bluetiger9/SmartElectronicLoad/Firmware/src/hw.cpp

#include "hw.h"

float HardwareValues::loadVoltageAdcMultiplier1;

float HardwareValues::loadVoltageAdcMultiplier2;

float HardwareValues::currentSenseAdcMultiplier;

float HardwareValues::currentSetDacMultiplier;
