bluetiger9/SmartElectronicLoad/Firmware/src/ota.h

/*
 * Copyright (c) 2025 by Attila Tőkés.
 *
 * Licence: MIT
 */
#ifndef OTA_H
#define OTA_H

#include <ArduinoOTA.h>

/** Handles Over-the-Air (OTA) firmware updates */
class OTA {
public:
  void begin() {
    Serial.println("Setting up OTA!");

    ArduinoOTA
      .onStart([]() {
        String type;
        if (ArduinoOTA.getCommand() == U_FLASH) {
            type = "sketch";
        } else {  // U_SPIFFS
            type = "filesystem";
        }

        // NOTE: if updating SPIFFS this would be the place to unmount SPIFFS using SPIFFS.end()
        Serial.println("Start updating " + type);
      })
      .onEnd([]() {
        Serial.println("\nEnd");
      })
      .onProgress([](unsigned int progress, unsigned int total) {
        if ((progress % 10 == 0) || (progress > 90)) {
          Serial.printf("Progress: %u%%\r", (progress / (total / 100)));
        }
      })
      .onError([](ota_error_t error) {
        Serial.printf("Error[%u]: ", error);
        if (error == OTA_AUTH_ERROR) {
            Serial.println("Auth Failed");
        } else if (error == OTA_BEGIN_ERROR) {
            Serial.println("Begin Failed");
        } else if (error == OTA_CONNECT_ERROR) {
            Serial.println("Connect Failed");
        } else if (error == OTA_RECEIVE_ERROR) {
            Serial.println("Receive Failed");
        } else if (error == OTA_END_ERROR) {
            Serial.println("End Failed");
        }
      });

    ArduinoOTA.begin();
  }

  void handle() {
    ArduinoOTA.handle();
  }

};

#endif
